TotallyNotAHackerTrustMeIAmADolphin/MPPT/src/PWM.c

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
/* Includes ------------------------------------------------------------------*/
#include "PWM.h"

/* USER CODE BEGIN Includes */
#include <stdint.h>
/* USER CODE END Includes */

TIM_HandleTypeDef htim1;
DMA_HandleTypeDef hdma_tim1_ch1;
DMA_HandleTypeDef hdma_tim1_ch2;

/* USER CODE BEGIN PV */
#define TIMER_PERIOD ((uint16_t)479) // 100 kHz PWM frequency
#define DITHER_TABLE_SIZE 8          // 3 bits of dithering
uint16_t aDitherTable1[2 * DITHER_TABLE_SIZE];
uint16_t aDitherTable2[2 * DITHER_TABLE_SIZE];
uint16_t maxDutyCycle = ((TIMER_PERIOD + 1) * DITHER_TABLE_SIZE) - 1;
uint8_t ditherBits = 3; // log2(DITHER_TABLE_SIZE)
/* USER CODE END PV */

void SystemClock_Config(void);
static void MX_GPIO_Init(void);
static void MX_DMA_Init(void);
static void MX_TIM1_Init(void);
/* USER CODE BEGIN PFP */
void initPWM(void);
// function to update the dithering table
void updateDitherTable(uint16_t *pDitherTable, uint16_t desiredDutyCycle);
// function to set the PWM
void setPWM(uint32_t channel, float dutyCyclePct);
/* USER CODE END PFP */

/**
 * @brief  The application entry point.
 * @retval int
 */
void initPWM(void)
{

  /* MCU Configuration--------------------------------------------------------*/

  /* Reset of all peripherals, Initializes the Flash interface and the Systick. */
  HAL_Init();

  /* Configure the system clock */
  SystemClock_Config();

  /* Initialize all configured peripherals */
  MX_GPIO_Init();
  MX_DMA_Init();
  MX_TIM1_Init();
  /* USER CODE BEGIN 2 */
  HAL_TIM_PWM_Start_DMA(&htim1, TIM_CHANNEL_1, (uint32_t *)aDitherTable1, 2 * DITHER_TABLE_SIZE);
  HAL_TIM_PWM_Start_DMA(&htim1, TIM_CHANNEL_2, (uint32_t *)aDitherTable2, 2 * DITHER_TABLE_SIZE);
  /* USER CODE END 2 */

  /* Infinite loop */
  /* USER CODE BEGIN WHILE */
  /* USER CODE END 3 */
}

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
/* USER CODE BEGIN 4 */
/**
 * @brief Updates the dithering table with the desired duty cycle in tics
 */
void updateDitherTable(uint16_t *pDitherTable, uint16_t desiredDutyCycle)
{
  if (desiredDutyCycle > maxDutyCycle)
  {
    desiredDutyCycle = maxDutyCycle;
  }

  uint16_t baseDutyCycle = desiredDutyCycle >> ditherBits;           // Upper 7 bits for base duty cycle
  uint16_t DitherIndex = desiredDutyCycle & ((1 << ditherBits) - 1); // Lower 3 bits for dither index

  for (uint16_t table_index = 0; table_index < DITHER_TABLE_SIZE; table_index++)
  {
    if (table_index < DitherIndex)
    {
      pDitherTable[table_index] = baseDutyCycle + 1;
    }
    else
    {
      pDitherTable[table_index] = baseDutyCycle;
    }
  }
}
/*
 * @brief Sets the PWM as value from 0 to 100 %
 */
void setPWM(uint32_t channel, float dutyCyclePct)
{
  if (dutyCyclePct < 0)
  {
    dutyCyclePct = 0;
  }
  else if (dutyCyclePct > 100)
  {
    dutyCyclePct = 100;
  }
  dutyCyclePct = dutyCyclePct / 100;

  uint16_t dutyCycle = (uint16_t)roundf(dutyCyclePct * (float)maxDutyCycle);

  if (channel == TIM_CHANNEL_1)
  {
    updateDitherTable(aDitherTable1, dutyCycle);
  }
  else if (channel == TIM_CHANNEL_2)
  {
    updateDitherTable(aDitherTable2, dutyCycle);
  }
}
/* USER CODE END 4 */
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
