TotallyNotAHackerTrustMeIAmADolphin/MPPT/Core/Src/comms.c

/**
  ******************************************************************************
  * @file           : comms.c
  * @brief          : Serial communication and telemetry implementation.
  ******************************************************************************
  */

#include "comms.h"
#include "controller.h"
#include "power.h"
#include "sensors.h"
#include "settings.h"
#include "mppt.h"
#include "usbd_cdc_if.h"
#include "system_config.h"
#include <stdio.h>
#include <string.h>
#include <stdlib.h>

/* Private variables */
static char cmdBuffer[64];
static uint8_t cmdIdx = 0;

void COMMS_Init(void) {
    memset(cmdBuffer, 0, sizeof(cmdBuffer));
    cmdIdx = 0;
}

void COMMS_SendTelemetry(const Measurements_t *m) {
    // Basic telemetry
    printf("{\"type\":\"telemetry\",\"Vin_mV\":%ld,\"Vout_mV\":%ld,\"Ain_mA\":%ld,\"Aout_mA\":%ld,\"Win_mW\":%ld,\"Wout_mW\":%ld,\"duty_x100\":%ld,\"mppt_step\":%ld,\"eff\":%d,\"temp_C\":%ld,\"state\":\"%s\",\"fault_reason\":\"%s\"}\n",
           m->voltageIn_mV, m->voltageOut_mV, m->currentIn_mA, m->currentOut_mA,
           m->powerIn_mW, m->powerOut_mW, POWER_PWM_GetDutyCycle_x100(), 
           MPPT_GetLastStep(),
           m->efficiency_x100 / 100, m->tempMCU_C_x100 / 100,
           CONTROLLER_GetStateString(),
           CONTROLLER_GetFaultReasonString());

    // Calibration raw data if active
    if (SETTINGS_IsCalibrating()) {
        uint32_t vIn, vOut, aIn, aOut;
        SENSORS_GetRawSums(&vIn, &vOut, &aIn, &aOut);
        printf("{\"type\":\"cal_raw\",\"Vin_raw\":%lu,\"Vout_raw\":%lu,\"Ain_raw\":%lu,\"Aout_raw\":%lu}\n",
               vIn / (ADC_SAMPLE_COUNT / 2), vOut / (ADC_SAMPLE_COUNT / 2),
               aIn / (ADC_SAMPLE_COUNT / 2), aOut / (ADC_SAMPLE_COUNT / 2));
    }
}

void COMMS_HandleCommands(void) {
    Calibration_t *cal = SETTINGS_GetCalibration();
    DeviceLimits_t *limits = SETTINGS_GetLimits();

    while (CDC_Available()) {
        uint8_t c = CDC_Read();
        if (c == '\n' || c == '\r') {
            if (cmdIdx > 0) {
                cmdBuffer[cmdIdx] = 0;
                
                if (strcmp(cmdBuffer, "CMD:CAL_ENTER") == 0) {
                    SETTINGS_SetCalibrating(true);
                    CONTROLLER_ResetFault(); // Clear any existing fault state
                    POWER_Start();           // Force power stage to enable MOE and DMA
                    printf("ACK:CAL_ENTER_OK\n");
                } else if (strcmp(cmdBuffer, "CMD:CAL_EXIT") == 0) {
                    SETTINGS_SetCalibrating(false);
                    printf("ACK:CAL_EXIT_OK\n");
                } else if (strcmp(cmdBuffer, "CMD:CAL_MODE_I") == 0) {
                    // No firmware-side effect: calibration now relies on an
                    // external wire bridging +BULK_IN to +BULK_OUT rather than
                    // a driven PWM state, so there's no "high side on" duty to
                    // switch to any more. Kept as a no-op ACK so the dashboard's
                    // existing calibration wizard (docs/app.js) still gets a
                    // response for this step.
                    printf("ACK:CAL_MODE_I_OK\n");
                } else if (strcmp(cmdBuffer, "CMD:CAL_MODE_V") == 0) {
                    printf("ACK:CAL_MODE_V_OK\n");
                } else if (strncmp(cmdBuffer, "CMD:CAL_I_LOW:", 14) == 0) {
                    uint32_t vIn, vOut, aIn, aOut;
                    SENSORS_GetRawSums(&vIn, &vOut, &aIn, &aOut);
                    cal->aInRawLow = (uint16_t)(aIn / (ADC_SAMPLE_COUNT / 2));
                    cal->aOutRawLow = (uint16_t)(aOut / (ADC_SAMPLE_COUNT / 2));
                    cal->aInRealLow_mA = cal->aOutRealLow_mA = (uint16_t)atoi(cmdBuffer + 14);
                    printf("ACK:CAL_I_LOW_OK:%d,%d\n", cal->aInRawLow, cal->aOutRawLow);
                } else if (strncmp(cmdBuffer, "CMD:CAL_I_HIGH:", 15) == 0) {
                    uint32_t vIn, vOut, aIn, aOut;
                    SENSORS_GetRawSums(&vIn, &vOut, &aIn, &aOut);
                    cal->aInRawHigh = (uint16_t)(aIn / (ADC_SAMPLE_COUNT / 2));
                    cal->aOutRawHigh = (uint16_t)(aOut / (ADC_SAMPLE_COUNT / 2));
                    cal->aInRealHigh_mA = cal->aOutRealHigh_mA = (uint16_t)atoi(cmdBuffer + 15);
                    printf("ACK:CAL_I_HIGH_OK:%d,%d\n", cal->aInRawHigh, cal->aOutRawHigh);
                } else if (strncmp(cmdBuffer, "CMD:CAL_V_LOW:", 14) == 0) {
                    uint32_t vIn, vOut, aIn, aOut;
                    SENSORS_GetRawSums(&vIn, &vOut, &aIn, &aOut);
                    cal->vInRawLow = (uint16_t)(vIn / (ADC_SAMPLE_COUNT / 2));
                    cal->vOutRawLow = (uint16_t)(vOut / (ADC_SAMPLE_COUNT / 2));
                    cal->vInRealLow_mV = cal->vOutRealLow_mV = (uint16_t)atoi(cmdBuffer + 14);
                    printf("ACK:CAL_V_LOW_OK:%d,%d\n", cal->vInRawLow, cal->vOutRawLow);
                } else if (strncmp(cmdBuffer, "CMD:CAL_V_HIGH:", 15) == 0) {
                    uint32_t vIn, vOut, aIn, aOut;
                    SENSORS_GetRawSums(&vIn, &vOut, &aIn, &aOut);
                    cal->vInRawHigh = (uint16_t)(vIn / (ADC_SAMPLE_COUNT / 2));
                    cal->vOutRawHigh = (uint16_t)(vOut / (ADC_SAMPLE_COUNT / 2));
                    cal->vInRealHigh_mV = cal->vOutRealHigh_mV = (uint16_t)atoi(cmdBuffer + 15);
                    printf("ACK:CAL_V_HIGH_OK:%d,%d\n", cal->vInRawHigh, cal->vOutRawHigh);
                } else if (strcmp(cmdBuffer, "CMD:CAL_SAVE") == 0) {
                    POWER_PWM_Set(0);
                    HAL_Delay(10);
                    SETTINGS_SaveCalibration();
                    printf("ACK:CAL_SAVE_OK\n");
                } else if (strncmp(cmdBuffer, "CMD:SET_V_MAX:", 14) == 0) {
                    limits->vOutMax_mV = constrain(atoi(cmdBuffer + 14), 0, HARD_LIMIT_VOUT_MAX_MV);
                    printf("ACK:SET_V_MAX_OK:%ld\n", limits->vOutMax_mV);
                } else if (strncmp(cmdBuffer, "CMD:SET_V_MIN:", 14) == 0) {
                    limits->vInMin_mV = constrain(atoi(cmdBuffer + 14), HARD_LIMIT_VIN_MIN_MV, HARD_LIMIT_VIN_MAX_MV);
                    printf("ACK:SET_V_MIN_OK:%ld\n", limits->vInMin_mV);
                } else if (strncmp(cmdBuffer, "CMD:SET_VIN_MAX:", 16) == 0) {
                    limits->vInMax_mV = constrain(atoi(cmdBuffer + 16), HARD_LIMIT_VIN_MIN_MV, HARD_LIMIT_VIN_MAX_MV);
                    printf("ACK:SET_VIN_MAX_OK:%ld\n", limits->vInMax_mV);
                } else if (strncmp(cmdBuffer, "CMD:SET_I_MAX:", 14) == 0) {
                    limits->iOutMax_mA = constrain(atoi(cmdBuffer + 14), 0, HARD_LIMIT_IOUT_MAX_MA);
                    printf("ACK:SET_I_MAX_OK:%ld\n", limits->iOutMax_mA);
                } else if (strncmp(cmdBuffer, "CMD:SET_I_MIN:", 14) == 0) {
                    limits->iOutMin_mA = constrain(atoi(cmdBuffer + 14), -HARD_LIMIT_IOUT_MAX_MA, HARD_LIMIT_IOUT_MAX_MA);
                    printf("ACK:SET_I_MIN_OK:%ld\n", limits->iOutMin_mA);
                } else if (strncmp(cmdBuffer, "CMD:SET_I_IN_MIN:", 17) == 0) {
                    limits->iInMin_mA = constrain(atoi(cmdBuffer + 17), -HARD_LIMIT_IIN_MAX_MA, HARD_LIMIT_IIN_MAX_MA);
                    printf("ACK:SET_I_IN_MIN_OK:%ld\n", limits->iInMin_mA);
                } else if (strncmp(cmdBuffer, "CMD:SET_MODE:", 13) == 0) {
                    int modeVal = atoi(cmdBuffer + 13);
                    if (modeVal >= MODE_MPPT && modeVal <= MODE_POWER_SUPPLY) {
                        limits->mode = (OperationMode_t)modeVal;
                        printf("ACK:SET_MODE_OK:%d\n", limits->mode);
                    } else {
                        printf("NACK:SET_MODE_INVALID:%d\n", modeVal);
                    }
                } else if (strcmp(cmdBuffer, "CMD:GET_LIMITS") == 0) {
                    printf("{\"type\":\"limits\",\"mode\":%d,\"Vmax\":%ld,\"Vmin\":%ld,\"VinMax\":%ld,\"Imax\":%ld,\"Imin\":%ld,\"IinMin\":%ld}\n",
                           limits->mode, limits->vOutMax_mV, limits->vInMin_mV, limits->vInMax_mV, limits->iOutMax_mA, limits->iOutMin_mA, limits->iInMin_mA);
                } else if (strcmp(cmdBuffer, "CMD:RESET_FAULT") == 0) {
                    CONTROLLER_ResetFault();
                    printf("ACK:RESET_FAULT_OK\n");
                } else if (strcmp(cmdBuffer, "CMD:LIMITS_SAVE") == 0) {
                    POWER_PWM_Set(0);
                    HAL_Delay(10);
                    SETTINGS_SaveLimits();
                    printf("ACK:LIMITS_SAVE_OK\n");
                } else if (strncmp(cmdBuffer, "CMD:TUNE_N:", 11) == 0) {
                    // Ignored (VSS Purged)
                    printf("ACK:TUNE_N_OK:0\n");
                } else if (strncmp(cmdBuffer, "CMD:TUNE_MIN:", 13) == 0) {
                    MPPT_SetStepSize(atoi(cmdBuffer + 13));
                    printf("ACK:TUNE_MIN_OK:%ld\n", MPPT_GetStepSize());
                } else if (strncmp(cmdBuffer, "CMD:TUNE_MAX:", 13) == 0) {
                    // Ignored (VSS Purged)
                    printf("ACK:TUNE_MAX_OK:2000\n");
                } else if (strncmp(cmdBuffer, "CMD:TUNE_THRESH:", 16) == 0) {
                    MPPT_SetThreshold((uint32_t)atoi(cmdBuffer + 16));
                    printf("ACK:TUNE_THRESH_OK:%lu\n", MPPT_GetThreshold());
                } else if (strncmp(cmdBuffer, "CMD:TUNE_INT:", 13) == 0) {
                    MPPT_SetInterval((uint32_t)atoi(cmdBuffer + 13));
                    printf("ACK:TUNE_INT_OK:%lu\n", MPPT_GetInterval());
                } else if (strncmp(cmdBuffer, "CMD:TUNE_EMA:", 13) == 0) {
                    SENSORS_SetEmaShift((uint8_t)atoi(cmdBuffer + 13));
                    printf("ACK:TUNE_EMA_OK:%d\n", SENSORS_GetEmaShift());
                } else if (strcmp(cmdBuffer, "CMD:TUNE_RESET") == 0) {
                    CONTROLLER_Reset();
                    printf("ACK:TUNE_RESET_OK\n");
                } else if (strcmp(cmdBuffer, "CMD:HELP") == 0) {
                    printf("Commands: CAL_..., SET_..., TUNE_STEP, TUNE_THRESH, TUNE_INT, TUNE_EMA, TUNE_RESET\n");
                }
                
                cmdIdx = 0;
            }
        } else if (cmdIdx < 63 && c != '\n' && c != '\r' && c != ' ') {
            cmdBuffer[cmdIdx++] = c;
        }
    }
}
