TotallyNotAHackerTrustMeIAmADolphin/MPPT/Core/Src/lcd_pcd8544.c

#include "lcd_pcd8544.h"
#include <string.h>

/* Minimal 5x7 Font */
static const uint8_t font_5x7[][5] = {
    {0x00, 0x00, 0x00, 0x00, 0x00}, // space
    {0x00, 0x00, 0x5f, 0x00, 0x00}, // !
    {0x00, 0x07, 0x00, 0x07, 0x00}, // "
    {0x14, 0x7f, 0x14, 0x7f, 0x14}, // #
    {0x24, 0x2a, 0x7f, 0x2a, 0x12}, // $
    {0x23, 0x13, 0x08, 0x64, 0x62}, // %
    {0x36, 0x49, 0x55, 0x22, 0x50}, // &
    {0x00, 0x05, 0x03, 0x00, 0x00}, // '
    {0x00, 0x1c, 0x22, 0x41, 0x00}, // (
    {0x00, 0x41, 0x22, 0x1c, 0x00}, // )
    {0x14, 0x08, 0x3e, 0x08, 0x14}, // *
    {0x08, 0x08, 0x3e, 0x08, 0x08}, // +
    {0x00, 0x50, 0x30, 0x00, 0x00}, // ,
    {0x08, 0x08, 0x08, 0x08, 0x08}, // -
    {0x00, 0x60, 0x60, 0x00, 0x00}, // .
    {0x20, 0x10, 0x08, 0x04, 0x02}, // /
    {0x3e, 0x51, 0x49, 0x45, 0x3e}, // 0
    {0x00, 0x42, 0x7f, 0x40, 0x00}, // 1
    {0x42, 0x61, 0x51, 0x49, 0x46}, // 2
    {0x21, 0x41, 0x45, 0x4b, 0x31}, // 3
    {0x18, 0x14, 0x12, 0x7f, 0x10}, // 4
    {0x27, 0x45, 0x45, 0x45, 0x39}, // 5
    {0x3c, 0x4a, 0x49, 0x49, 0x30}, // 6
    {0x01, 0x71, 0x09, 0x05, 0x03}, // 7
    {0x36, 0x49, 0x49, 0x49, 0x36}, // 8
    {0x06, 0x49, 0x49, 0x29, 0x1e}, // 9
    {0x00, 0x36, 0x36, 0x00, 0x00}, // :
    {0x00, 0x56, 0x36, 0x00, 0x00}, // ;
    {0x08, 0x14, 0x22, 0x41, 0x00}, // <
    {0x14, 0x14, 0x14, 0x14, 0x14}, // =
    {0x00, 0x41, 0x22, 0x14, 0x08}, // >
    {0x02, 0x01, 0x51, 0x09, 0x06}, // ?
    {0x32, 0x49, 0x79, 0x41, 0x3e}, // @
    {0x7e, 0x11, 0x11, 0x11, 0x7e}, // A
    {0x7f, 0x49, 0x49, 0x49, 0x36}, // B
    {0x3e, 0x41, 0x41, 0x41, 0x22}, // C
    {0x7f, 0x41, 0x41, 0x22, 0x1c}, // D
    {0x7f, 0x49, 0x49, 0x49, 0x41}, // E
    {0x7f, 0x09, 0x09, 0x09, 0x01}, // F
    {0x3e, 0x41, 0x49, 0x49, 0x7a}, // G
    {0x7f, 0x08, 0x08, 0x08, 0x7f}, // H
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
    {0x00, 0x41, 0x7f, 0x41, 0x00}, // [ (mapped to I)
    {0x20, 0x10, 0x08, 0x04, 0x02}, // backslash
    {0x00, 0x41, 0x7f, 0x41, 0x00}, // ] (mapped to I)
    {0x04, 0x02, 0x01, 0x02, 0x04}, // ^
    {0x40, 0x40, 0x40, 0x40, 0x40}, // _
    {0x00, 0x01, 0x02, 0x04, 0x00}, // `
    {0x20, 0x54, 0x54, 0x54, 0x78}, // a
    {0x7f, 0x48, 0x44, 0x44, 0x38}, // b
    {0x38, 0x44, 0x44, 0x44, 0x20}, // c
    {0x38, 0x44, 0x44, 0x48, 0x7f}, // d
    {0x38, 0x54, 0x54, 0x54, 0x18}, // e
    {0x08, 0x7e, 0x09, 0x01, 0x02}, // f
    {0x0c, 0x52, 0x52, 0x52, 0x3e}, // g
    {0x7f, 0x08, 0x04, 0x04, 0x78}, // h
    {0x00, 0x44, 0x7d, 0x40, 0x00}, // i
    {0x20, 0x40, 0x44, 0x3d, 0x00}, // j
    {0x7f, 0x10, 0x28, 0x44, 0x00}, // k
    {0x00, 0x41, 0x7f, 0x40, 0x00}, // l
    {0x7c, 0x04, 0x18, 0x04, 0x78}, // m
    {0x7c, 0x08, 0x04, 0x04, 0x78}, // n
    {0x38, 0x44, 0x44, 0x44, 0x38}, // o
    {0x7c, 0x14, 0x14, 0x14, 0x08}, // p
    {0x08, 0x14, 0x14, 0x18, 0x7c}, // q
    {0x7c, 0x08, 0x04, 0x04, 0x08}, // r
    {0x48, 0x54, 0x54, 0x54, 0x20}, // s
    {0x04, 0x3f, 0x44, 0x40, 0x20}, // t
    {0x3c, 0x40, 0x40, 0x20, 0x7c}, // u
    {0x1c, 0x20, 0x40, 0x20, 0x1c}, // v
    {0x3c, 0x40, 0x30, 0x40, 0x3c}, // w
    {0x44, 0x28, 0x10, 0x28, 0x44}, // x
    {0x0c, 0x50, 0x50, 0x50, 0x3c}, // y
    {0x44, 0x64, 0x54, 0x4c, 0x44}, // z
};

static void LCD_Write(LCD_Handle_t *hlcd, uint8_t data, uint8_t mode) {
    HAL_GPIO_WritePin(hlcd->port_dc, hlcd->pin_dc, mode); // 0 = Command, 1 = Data
    HAL_GPIO_WritePin(hlcd->port_ce, hlcd->pin_ce, GPIO_PIN_RESET);
    
    HAL_SPI_Transmit(hlcd->hspi, &data, 1, 10);
    
    // Ensure SPI is not busy before raising CE
    while (HAL_SPI_GetState(hlcd->hspi) == HAL_SPI_STATE_BUSY);
    HAL_GPIO_WritePin(hlcd->port_ce, hlcd->pin_ce, GPIO_PIN_SET);
}

void LCD_Init(LCD_Handle_t *hlcd) {
    /* Hard Reset */
    HAL_GPIO_WritePin(hlcd->port_rst, hlcd->pin_rst, GPIO_PIN_RESET);
    HAL_Delay(20); // Longer reset
    HAL_GPIO_WritePin(hlcd->port_rst, hlcd->pin_rst, GPIO_PIN_SET);
    HAL_Delay(20);

    /* PCD8544 Initialization Sequence */
    LCD_Write(hlcd, 0x21, 0); // Extended instructions (H=1)
    LCD_Write(hlcd, 0xA8, 0); // Set VOP (Contrast) - 0xA8 is very safe/low
    LCD_Write(hlcd, 0x04, 0); // Temp coefficient
    LCD_Write(hlcd, 0x14, 0); // Bias mode 1:48
    LCD_Write(hlcd, 0x20, 0); // Basic instructions (H=0, Horizontal)
    LCD_Write(hlcd, 0x0C, 0); // Normal display mode

    LCD_Clear(hlcd);
    LCD_Update(hlcd);
}

void LCD_Clear(LCD_Handle_t *hlcd) {
    memset(hlcd->buffer, 0, LCD_BUFFER_SIZE);
}

void LCD_Update(LCD_Handle_t *hlcd) {
    LCD_Write(hlcd, 0x80, 0); // Set X address to 0
    LCD_Write(hlcd, 0x40, 0); // Set Y address to 0
    
    HAL_GPIO_WritePin(hlcd->port_dc, hlcd->pin_dc, 1); // Data mode
    HAL_GPIO_WritePin(hlcd->port_ce, hlcd->pin_ce, GPIO_PIN_RESET);
    
    HAL_SPI_Transmit(hlcd->hspi, hlcd->buffer, LCD_BUFFER_SIZE, 100);
    
    while (HAL_SPI_GetState(hlcd->hspi) == HAL_SPI_STATE_BUSY);
    HAL_GPIO_WritePin(hlcd->port_ce, hlcd->pin_ce, GPIO_PIN_SET);
}

void LCD_DrawPixel(LCD_Handle_t *hlcd, uint8_t x, uint8_t y, bool on) {
    if (x >= LCD_WIDTH || y >= LCD_HEIGHT) return;
    
    uint16_t index = x + (y / 8) * LCD_WIDTH;
    if (on) {
        hlcd->buffer[index] |= (1 << (y % 8));
    } else {
        hlcd->buffer[index] &= ~(1 << (y % 8));
    }
}

void LCD_DrawString(LCD_Handle_t *hlcd, uint8_t x, uint8_t y, const char *str) {
    while (*str) {
        uint8_t c = *str;
        if (c < 32 || c > 126) c = ' '; // Map to space if out of range
        
        // Safety: If we go past the end of our current table (z), map to '?'
        if (c - 32 >= (sizeof(font_5x7)/sizeof(font_5x7[0]))) {
            c = '?';
        }
        
        c -= 32; // Offset for font table

        // Each character in the font table is 5 bytes wide
        for (uint8_t i = 0; i < 5; i++) {
            uint8_t column = font_5x7[c][i];
            for (uint8_t j = 0; j < 8; j++) {
                if (column & (1 << j)) {
                    LCD_DrawPixel(hlcd, x + i, y + j, true);
                } else {
                    LCD_DrawPixel(hlcd, x + i, y + j, false);
                }
            }
        }
        
        // Add 1-pixel space between characters
        for (uint8_t j = 0; j < 8; j++) {
            LCD_DrawPixel(hlcd, x + 5, y + j, false);
        }

        str++;
        x += 6; // Move to next character (5 pixels + 1 space)
        if (x > LCD_WIDTH - 6) break;
    }
}
