TotallyNotAHackerTrustMeIAmADolphin/MPPT/Core/Inc/mppt.h

/**
  ******************************************************************************
  * @file           : mppt.h
  * @brief          : Header for MPPT algorithms (P&O and Sweep).
  ******************************************************************************
  */

#ifndef __MPPT_H
#define __MPPT_H

#include "system_types.h"

/* Algorithm Selection */
#define MPPT_ALGO_P_AND_O       0
#define MPPT_ALGO_INC_COND      1

/* Set the active algorithm here for easy switching */
#define ACTIVE_MPPT_ALGO        MPPT_ALGO_INC_COND

/**
 * @brief Performs a single step of the Perturb and Observe algorithm.
 * @param m Pointer to current measurements.
 * @param limits Pointer to system operational limits.
 * @return The required duty cycle CHANGE (delta) in ticks.
 */
int32_t MPPT_PerturbAndObserve(const Measurements_t *m, const DeviceLimits_t *limits);

/**
 * @brief Performs a single step of the Incremental Conductance algorithm.
 * @param m Pointer to current measurements.
 * @param limits Pointer to system operational limits.
 * @return The required duty cycle CHANGE (delta) in ticks.
 */
int32_t MPPT_IncrementalConductance(const Measurements_t *m, const DeviceLimits_t *limits);

/**
 * @brief Manages the global power sweep.
 * @param m Pointer to current measurements.
 * @param limits Pointer to system operational limits.
 * @param isFinished Pointer to a bool set to true when sweep is done.
 * @return The current sweep duty cycle in ticks.
 */
int32_t MPPT_RunSweep(const Measurements_t *m, const DeviceLimits_t *limits, bool *isFinished);

/**
 * @brief Resets the sweep internal state.
 * @param startDuty The initial duty cycle to start the sweep from.
 */
void MPPT_ResetSweep(int32_t startDuty);

/**
 * @brief Initializes the P&O tracking baseline with the current power measurement.
 * @param m Pointer to current measurements.
 */
void MPPT_StartTracking(const Measurements_t *m);

/**
 * @brief Returns the last calculated step size (ticks).
 */
int32_t MPPT_GetLastStep(void);

/* Dynamic Tuning Interface */
void MPPT_SetStepSize(int32_t step);
void MPPT_SetThreshold(uint32_t uw);
void MPPT_SetInterval(uint32_t ms);

int32_t MPPT_GetStepSize(void);
uint32_t MPPT_GetThreshold(void);
uint32_t MPPT_GetInterval(void);

#endif /* __MPPT_H */
